SmartFuseBox/SmartFuseBox/KiCad/SmartFuseBox/sheets/Relays.kicad_sch

## KiCad design KiCad/SmartFuseBox/sheets/Relays.kicad_sch (2026-03-11)

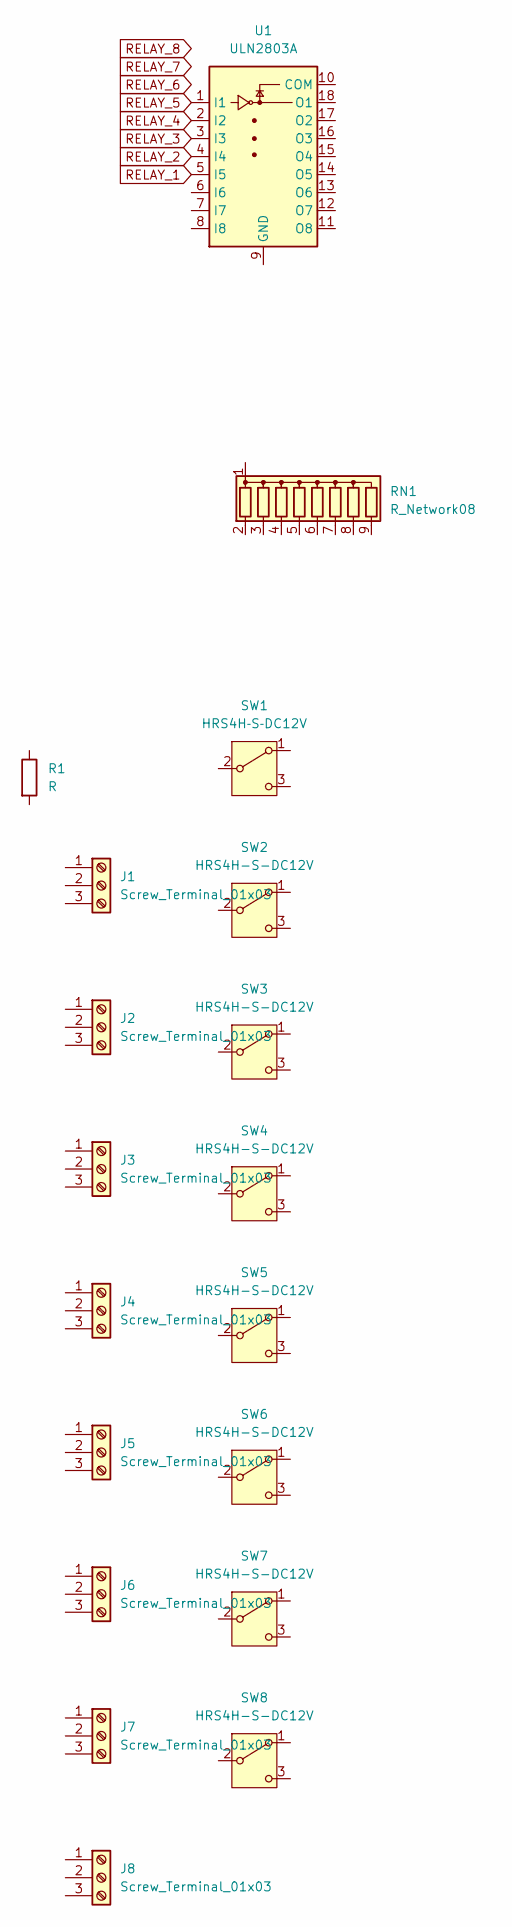
[picture p5: schematic Relays.kicad_sch]

Parts:
J1, J2, J3, J4, J5, J6, J7, J8: Screw_Terminal_01x03
R1: R
RN1: R_Network08; R_Array_SIP9
SW1: HRS4H‑S‑DC12V
SW2, SW3, SW4, SW5, SW6, SW7, SW8: HRS4H-S-DC12V
U1: ULN2803A

Connections:
RELAY_1: U1.5 (I5)
RELAY_2: U1.4 (I4)
RELAY_3: U1.3 (I3)
RELAY_4: U1.2 (I2)
RELAY_5: U1.1 (I1)
