SmartFuseBox/SmartFuseBox/PowerControlHub/PowerControlHub.ino

/*
 * PowerControlHub
 * Copyright (C) 2025 Simon Carter (s1cart3r@gmail.com)
 *
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
 * You should have received a copy of the GNU General Public License
 * along with this program. If not, see <https://www.gnu.org/licenses/>.
 */
#include <Arduino.h>
#include <SerialCommandManager.h>

#include "Local.h"
#include "PowerControlHubApp.h"
#include "SystemFunctions.h"

#include "WaterSensorHandler.h"
#include "Dht11SensorHandler.h"
#include "LightSensorHandler.h"
#include "SystemSensorHandler.h"

 // Hardware UART selection. Change this define if your board routes its serial
// port differently.
// COMPUTER_SERIAL – connected to the host PC / debug monitor.
#define COMPUTER_SERIAL Serial

// forward declares
void onComputerCommandReceived(SerialCommandManager* mgr);


// Consumer note:
// - `commandMgrComputer` is local to your .ino so you can select the hardware
//   Serial instance and baud rate appropriate for your board. Keep the callback
//   `onComputerCommandReceived` in this file so it can access the serial manager.
// - Construct `PowerControlHubApp` with a pointer to the serial manager, then
//   call `app.setup()`. GPS and Nextion serial ports are initialised automatically
//   from persisted config (SensorEntry pins/uartNum and NextionConfig respectively).
// - Call `app.loop()` from `loop()`.

SerialCommandManager commandMgrComputer(&COMPUTER_SERIAL, onComputerCommandReceived, '\n', ':', ';', '=', 500, 64);

PowerControlHubApp app(&commandMgrComputer);

void powerControlHubTask(void* pvParameters)
{
	PowerControlHubApp* app = (PowerControlHubApp*)pvParameters;
	while (true)
	{
		app->loop();
		vTaskDelay(1);
	}
}

void setup()
{
	// Serial initialization is performed first to ensure that any logging or error messages
	// from DateTimeManager or ConfigManager during initialization are properly output.
	SystemFunctions::initializeSerial(COMPUTER_SERIAL, 115200, true);

	SystemFunctions::configureAdc();

	// configure app
	app.setup(nullptr, 0);

	// Create a dedicated task with 16KB stack
	xTaskCreatePinnedToCore(
		powerControlHubTask,
		"PowerControlHub",
		16384,           // stack size
		&app,            // parameters
		1,               // priority
		NULL,            // task handle
		1                // core 1
	);
}

void loop()
{
	vTaskDelay(portMAX_DELAY);
}

// Called when a command arrives on COMPUTER_SERIAL that no registered handler
// claimed. Reports the unrecognised message back to the sender as an error and
// resets the serial buffer to discard any partial frame that may follow.
void onComputerCommandReceived(SerialCommandManager* mgr)
{
	commandMgrComputer.sendError(mgr->getRawMessage(), F("STATCMD"));
	SystemFunctions::resetSerial(COMPUTER_SERIAL);
}
