SmartFuseBox/SmartFuseBox/PowerControlHub/ConfigController.cpp

/*
 * PowerControlHub
 * Copyright (C) 2025 Simon Carter (s1cart3r@gmail.com)
 *
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
 * You should have received a copy of the GNU General Public License
 * along with this program. If not, see <https://www.gnu.org/licenses/>.
 */
#include "ConfigController.h"
#include "SystemDefinitions.h"
#include "RelayController.h"
#include "IBluetoothRadio.h"
#include "IWifiController.h"
#include "SystemFunctions.h"
#include "DateTimeManager.h"

// from NextionIds.h
constexpr uint8_t ImageButtonColorBlue = 2;
constexpr uint8_t ImageButtonColorYellow = 7;


ConfigController::ConfigController(SoundController* soundController, 
	IBluetoothRadio* bluetoothRadio,
	IWifiController* wifiController)
	: _soundController(soundController),
	_bluetoothRadio(bluetoothRadio),
	_wifiController(wifiController),
	_config(nullptr)
{
	_config = ConfigManager::getConfigPtr();
}

Config* ConfigController::getConfigPtr()
{
	return _config;
}

ConfigResult ConfigController::save()
{
	if (_config == nullptr)
		return ConfigResult::InvalidConfig;

	return ConfigManager::save() ? ConfigResult::Success : ConfigResult::Failed;
}

ConfigResult ConfigController::reset()
{
	if (_config == nullptr)
		return ConfigResult::InvalidConfig;

	ConfigManager::resetToDefaults();
	return ConfigResult::Success;
}

ConfigResult ConfigController::rename(const char* name)
{
	if (_config == nullptr)
		return ConfigResult::InvalidConfig;

	if (name == nullptr)
		return ConfigResult::InvalidParameter;

	if (strlen(name) > ConfigMaxNameLength)
		return ConfigResult::TooLong;

	strncpy(_config->location.name, name, sizeof(_config->location.name) - 1);
	_config->location.name[sizeof(_config->location.name) - 1] = '\0';
	return ConfigResult::Success;
}

ConfigResult ConfigController::mapHomeButton(const uint8_t homeButtonIndex, const uint8_t relayIndex)
{
	if (_config == nullptr)
		return ConfigResult::InvalidCommand;

	if (homeButtonIndex >= ConfigHomeButtons)
		return ConfigResult::InvalidParameter;
	
	if (relayIndex >= ConfigRelayCount)
		return ConfigResult::InvalidRelay;

	_config->relay.homePageMapping[homeButtonIndex] = relayIndex;
	return ConfigResult::Success;
}

ConfigResult ConfigController::setLocationType(const uint8_t locationlType)
{
	if (_config == nullptr)
		return ConfigResult::InvalidConfig;
	_config->location.locationType = static_cast<LocationType>(locationlType);
	updateSoundControllerConfig();
	return ConfigResult::Success;
}

void ConfigController::updateSoundControllerConfig()
{
	if (_soundController != nullptr && _config != nullptr)
	{
		_soundController->configUpdated(_config);
	}
}

ConfigResult ConfigController::setsoundDelayStart(const uint16_t delayMilliSeconds)
{
	if (_config == nullptr)
		return ConfigResult::InvalidConfig;

	_config->sound.startDelayMs = delayMilliSeconds;
	updateSoundControllerConfig();
	return ConfigResult::Success;
}

ConfigResult ConfigController::setBluetoothEnabled(const bool enabled)
{
	if (_config == nullptr)
		return ConfigResult::InvalidConfig;

	_config->network.bluetoothEnabled = enabled;

	// do not apply live, only on next restart, otherwise too many enabled/disable cycles will 
	// eventually force the board to run out of memory, the only exception to this is if 
	// it starts disabled and is being enabled now, i.e. once on it needs rebooting to turn off again
	if (_bluetoothRadio && !_bluetoothRadio->isEnabled())
	{
		if (!_bluetoothRadio->setEnabled(enabled))
		{
			return ConfigResult::BluetoothInitFailed;
		}
	}

	return ConfigResult::Success;
}

ConfigResult ConfigController::setWifiEnabled(const bool enabled)
{
	if (_config == nullptr)
		return ConfigResult::InvalidConfig;

	_config->network.wifiEnabled = enabled;

	// do not apply live, only on next restart, otherwise too many enabled/disable cycles will 
	// eventually force the board to run out of memory, the only exception to this is if 
	// it starts disabled and is being enabled now, i.e. once on it needs rebooting to turn off again
	if (_wifiController && !_wifiController->isEnabled())
	{
		if (!_wifiController->setEnabled(enabled))
		{
			return ConfigResult::WifiInitFailed;
		}
	}

	return ConfigResult::Success;
}

ConfigResult ConfigController::setWifiAccessMode(const WifiMode accessMode)
{
	if (_config == nullptr)
		return ConfigResult::InvalidConfig;

	// only accept supported WiFi modes to avoid persisting invalid values from user input
	if (accessMode != WifiMode::AccessPoint && accessMode != WifiMode::Client)
		return ConfigResult::InvalidParameter;
	_config->network.accessMode = accessMode;
	return ConfigResult::Success;
}

ConfigResult ConfigController::setWifiSsid(const char* ssid)
{
	if (_config == nullptr || ssid == nullptr)
		return ConfigResult::InvalidConfig;

	if (strlen(ssid) > MaxSSIDLength - 1)
		return ConfigResult::TooLong;

	strncpy(_config->network.ssid, ssid, sizeof(_config->network.ssid) - 1);
	_config->network.ssid[sizeof(_config->network.ssid) - 1] = '\0';
	return ConfigResult::Success;
}

ConfigResult ConfigController::setWifiPassword(const char* password)
{
	if (_config == nullptr)
		return ConfigResult::InvalidConfig;

	if (password == nullptr)
		return ConfigResult::InvalidParameter;

	if (strlen(password) > MaxWiFiPasswordLength - 1)
		return ConfigResult::InvalidParameter;

	strncpy(_config->network.password, password, sizeof(_config->network.password) - 1);
	_config->network.password[sizeof(_config->network.password) - 1] = '\0';
	return ConfigResult::Success;
}

ConfigResult ConfigController::setWifiPort(const uint16_t port)
{
	if (_config == nullptr)
		return ConfigResult::InvalidConfig;

	if (port == 0)
	{
		return ConfigResult::InvalidParameter;
	}

	_config->network.port = port;
	return ConfigResult::Success;
}

ConfigResult ConfigController::setWifiIpAddress(const char* ipAddress)
{
	if (_config == nullptr)
		return ConfigResult::InvalidConfig;

	if (ipAddress == nullptr)
		return ConfigResult::InvalidParameter;

	if (strlen(ipAddress) > MaxIpAddressLength - 1)
		return ConfigResult::TooLong;

	IPAddress ip;
	if (!ip.fromString(ipAddress))
	{
		return ConfigResult::InvalidParameter;
	}

	strncpy(_config->network.apIpAddress, ipAddress, sizeof(_config->network.apIpAddress) - 1);
	_config->network.apIpAddress[sizeof(_config->network.apIpAddress) - 1] = '\0';
	return ConfigResult::Success;
}

// C20: Set timezone offset
ConfigResult ConfigController::setTimezoneOffset(const int8_t offset)
{
	if (_config == nullptr)
		return ConfigResult::InvalidConfig;

	// Validate range: -12 to +14 hours
	if (offset < -12 || offset > 14)
		return ConfigResult::InvalidParameter;

	_config->system.timezoneOffset = offset;
	DateTimeManager::setTimezoneOffset(offset);
	return ConfigResult::Success;
}

// C21: Set MMSI
ConfigResult ConfigController::setMmsi(const char* mmsi)
{
	if (_config == nullptr)
		return ConfigResult::InvalidConfig;

	if (mmsi == nullptr)
		return ConfigResult::InvalidParameter;

	// Validate MMSI is exactly 9 digits
	size_t len = strlen(mmsi);
	if (len != 9)
		return ConfigResult::InvalidParameter;

	for (size_t i = 0; i < len; i++)
	{
		if (!isdigit(mmsi[i]))
			return ConfigResult::InvalidParameter;
	}

	strncpy(_config->location.mmsi, mmsi, sizeof(_config->location.mmsi) - 1);
	_config->location.mmsi[sizeof(_config->location.mmsi) - 1] = '\0';
	return ConfigResult::Success;
}

// C22: Set call sign
ConfigResult ConfigController::setCallSign(const char* callSign)
{
	if (_config == nullptr)
		return ConfigResult::InvalidConfig;

	if (callSign == nullptr)
		return ConfigResult::InvalidParameter;

	strncpy(_config->location.callSign, callSign, sizeof(_config->location.callSign) - 1);
	_config->location.callSign[sizeof(_config->location.callSign) - 1] = '\0';
	return ConfigResult::Success;
}

// C23: Set home port
ConfigResult ConfigController::setHomePort(const char* homePort)
{
	if (_config == nullptr)
		return ConfigResult::InvalidConfig;

	if (homePort == nullptr)
		return ConfigResult::InvalidParameter;

	strncpy(_config->location.homePort, homePort, sizeof(_config->location.homePort) - 1);
	_config->location.homePort[sizeof(_config->location.homePort) - 1] = '\0';
	return ConfigResult::Success;
}

// C24: Set LED RGB color
ConfigResult ConfigController::setLedColor(const uint8_t type, const uint8_t colorSet, 
										   const uint8_t r, const uint8_t g, const uint8_t b)
{
	if (_config == nullptr)
		return ConfigResult::InvalidConfig;

	// type: 0=day, 1=night
	// colorSet: 0=good, 1=bad
	if (type > 1 || colorSet > 1)
		return ConfigResult::InvalidParameter;

	if (type == 0) // Day mode
	{
		if (colorSet == 0) // Good color
		{
			_config->led.dayGoodColor[0] = r;
			_config->led.dayGoodColor[1] = g;
			_config->led.dayGoodColor[2] = b;
		}
		else // Bad color
		{
			_config->led.dayBadColor[0] = r;
			_config->led.dayBadColor[1] = g;
			_config->led.dayBadColor[2] = b;
		}
	}
	else // Night mode
	{
		if (colorSet == 0) // Good color
		{
			_config->led.nightGoodColor[0] = r;
			_config->led.nightGoodColor[1] = g;
			_config->led.nightGoodColor[2] = b;
		}
		else // Bad color
		{
			_config->led.nightBadColor[0] = r;
			_config->led.nightBadColor[1] = g;
			_config->led.nightBadColor[2] = b;
		}
	}

	return ConfigResult::Success;
}

// C25: Set LED brightness
ConfigResult ConfigController::setLedBrightness(const uint8_t type, const uint8_t brightness)
{
	if (_config == nullptr)
		return ConfigResult::InvalidConfig;

	// type: 0=day, 1=night
	// brightness: 0-100
	if (type > 1 || brightness > 100)
		return ConfigResult::InvalidParameter;

	if (type == 0)
		_config->led.dayBrightness = brightness;
	else
		_config->led.nightBrightness = brightness;

	return ConfigResult::Success;
}

// C26: Set LED auto-switch
ConfigResult ConfigController::setLedAutoSwitch(const bool enabled)
{
	if (_config == nullptr)
		return ConfigResult::InvalidConfig;

	_config->led.autoSwitch = enabled;
	return ConfigResult::Success;
}

// C27: Set LED enable states
ConfigResult ConfigController::setLedEnableStates(const bool gps, const bool warning, const bool system)
{
	if (_config == nullptr)
		return ConfigResult::InvalidConfig;

	_config->led.gpsEnabled = gps;
	_config->led.warningEnabled = warning;
	_config->led.systemEnabled = system;

	return ConfigResult::Success;
}

// C28: Set control panel tones
ConfigResult ConfigController::setControlPanelTones(const uint8_t type, const uint8_t preset, 
													const uint16_t toneHz, const uint16_t durationMs, 
													const uint32_t repeatMs)
{
	if (_config == nullptr)
		return ConfigResult::InvalidConfig;

	// type: 0=good, 1=bad
	if (type > 1)
		return ConfigResult::InvalidParameter;

	// preset: 0=custom, 1=submarine ping, 2=double beep, 3=rising chirp, 
	//         4=descending alert, 5=nautical bell, 0xFFFF=no sound
	// For preset validation, we allow 0-5 or 0xFFFF (65535)
	if (preset > 5 && preset != 0xFF)
		return ConfigResult::InvalidParameter;

	if (type == 0) // Good tone
	{
		_config->sound.goodPreset = preset;
		_config->sound.goodToneHz = toneHz;
		_config->sound.goodDurationMs = durationMs;
		// repeat is only for bad sounds, ignore for good
	}
	else // Bad tone
	{
		_config->sound.badPreset = preset;
		_config->sound.badToneHz = toneHz;
		_config->sound.badDurationMs = durationMs;
		_config->sound.badRepeatMs = repeatMs;
	}

	return ConfigResult::Success;
}

// C31: Set SD card initialize speed
ConfigResult ConfigController::setSdCardInitializeSpeed(const uint8_t speedMhz)
{
	if (_config == nullptr)
		return ConfigResult::InvalidConfig;

	// Only allow specific valid speeds: 4, 8, 12, 16, 20, 24 MHz
	if (speedMhz != 4 && speedMhz != 8 && speedMhz != 12 && 
		speedMhz != 16 && speedMhz != 20 && speedMhz != 24)
		return ConfigResult::InvalidParameter;

	_config->sdCard.initializeSpeed = speedMhz;
	return ConfigResult::Success;
}

// C32: Set SD card CS pin
ConfigResult ConfigController::setSdCardCsPin(const uint8_t csPin)
{
	if (_config == nullptr)
		return ConfigResult::InvalidConfig;

	if (PinGuard::isBlocked(PinGuard::validate(csPin, PinUse::SpiCs)))
		return ConfigResult::InvalidPin;

	_config->sdCard.csPin = csPin;
	return ConfigResult::Success;
}

// C4: Set SPI pins
ConfigResult ConfigController::setSpiPins(const uint8_t sckPin, const uint8_t mosiPin, const uint8_t misoPin)
{
	if (_config == nullptr)
		return ConfigResult::InvalidConfig;

	if (PinGuard::isBlocked(PinGuard::validate(sckPin, PinUse::SpiSck)) ||
		PinGuard::isBlocked(PinGuard::validate(mosiPin, PinUse::SpiMosi)) ||
		PinGuard::isBlocked(PinGuard::validate(misoPin, PinUse::SpiMiso)))
	{
		return ConfigResult::InvalidPin;
	}

	_config->spiPins.sckPin = sckPin;
	_config->spiPins.mosiPin = mosiPin;
	_config->spiPins.misoPin = misoPin;
	return ConfigResult::Success;
}

// C33: Set light sensor daytime threshold
ConfigResult ConfigController::setLightSensorThreshold(const uint16_t threshold)
{
	if (_config == nullptr)
		return ConfigResult::InvalidConfig;

	if (threshold > 1023)
		return ConfigResult::InvalidParameter;

	_config->lightSensor.daytimeThreshold = threshold;
	return ConfigResult::Success;
}

// C6: Set XpdzTone pin
ConfigResult ConfigController::setXpdzTonePin(const uint8_t pin)
{
	if (_config == nullptr)
		return ConfigResult::InvalidConfig;

	if (PinGuard::isBlocked(PinGuard::validate(pin, PinUse::Output)))
		return ConfigResult::InvalidPin;

	_config->xpdzTone.pin = pin;
	return ConfigResult::Success;
}

// C8: Set Hw479Rgb RGB LED pins
ConfigResult ConfigController::setHw479RgbPins(const uint8_t rPin, const uint8_t gPin, const uint8_t bPin)
{
	if (_config == nullptr)
		return ConfigResult::InvalidConfig;

	if (PinGuard::isBlocked(PinGuard::validate(rPin, PinUse::Output)) ||
		PinGuard::isBlocked(PinGuard::validate(gPin, PinUse::Output)) ||
		PinGuard::isBlocked(PinGuard::validate(bPin, PinUse::Output)))
	{
		return ConfigResult::InvalidPin;
	}

	_config->hw479Rgb.rPin = rPin;
	_config->hw479Rgb.gPin = gPin;
	_config->hw479Rgb.bPin = bPin;
	return ConfigResult::Success;
}

// C18: Set RtcConfig DS1302 pins
ConfigResult ConfigController::setRtcPins(const uint8_t dataPin, const uint8_t clockPin, const uint8_t resetPin)
{
	if (_config == nullptr)
		return ConfigResult::InvalidConfig;

	// Temporarily clear current RTC pin assignments so they don't
	// conflict with themselves during validation (getUsedPins collects
	// the current rtc.dataPin/clockPin/resetPin values).
	const uint8_t oldData = _config->rtc.dataPin;
	const uint8_t oldClock = _config->rtc.clockPin;
	const uint8_t oldReset = _config->rtc.resetPin;

	_config->rtc.dataPin = PinDisabled;
	_config->rtc.clockPin = PinDisabled;
	_config->rtc.resetPin = PinDisabled;

	const bool blocked = PinGuard::isBlocked(PinGuard::validate(dataPin, PinUse::Output))
		|| PinGuard::isBlocked(PinGuard::validate(clockPin, PinUse::Output))
		|| PinGuard::isBlocked(PinGuard::validate(resetPin, PinUse::Output));

	if (blocked)
	{
		// Restore old values on failure
		_config->rtc.dataPin = oldData;
		_config->rtc.clockPin = oldClock;
		_config->rtc.resetPin = oldReset;
		return ConfigResult::InvalidPin;
	}

	_config->rtc.dataPin = dataPin;
	_config->rtc.clockPin = clockPin;
	_config->rtc.resetPin = resetPin;
	return ConfigResult::Success;
}

// C19 (N commands): Set NextionConfig display configuration — individual setters
ConfigResult ConfigController::setNextionEnabled(const bool enabled)
{
	if (_config == nullptr)
		return ConfigResult::InvalidConfig;

	_config->nextion.enabled = enabled;
	return ConfigResult::Success;
}

ConfigResult ConfigController::setNextionHardwareSerial(const bool isHardwareSerial)
{
	if (_config == nullptr)
		return ConfigResult::InvalidConfig;

	_config->nextion.isHardwareSerial = isHardwareSerial;
	return ConfigResult::Success;
}

ConfigResult ConfigController::setNextionRxPin(const uint8_t rxPin)
{
	if (_config == nullptr)
		return ConfigResult::InvalidConfig;

	if (PinGuard::isBlocked(PinGuard::validate(rxPin, PinUse::Input)))
		return ConfigResult::InvalidPin;

	_config->nextion.rxPin = rxPin;
	return ConfigResult::Success;
}

ConfigResult ConfigController::setNextionTxPin(const uint8_t txPin)
{
	if (_config == nullptr)
		return ConfigResult::InvalidConfig;

	if (PinGuard::isBlocked(PinGuard::validate(txPin, PinUse::Output)))
		return ConfigResult::InvalidPin;

	_config->nextion.txPin = txPin;
	return ConfigResult::Success;
}

ConfigResult ConfigController::setNextionBaudRate(const uint32_t baudRate)
{
	if (_config == nullptr)
		return ConfigResult::InvalidConfig;

	_config->nextion.baudRate = baudRate;
	return ConfigResult::Success;
}

ConfigResult ConfigController::setNextionUartNum(const uint8_t uartNum)
{
    if (_config == nullptr)
        return ConfigResult::InvalidConfig;

    if (uartNum != 1 && uartNum != 2)
        return ConfigResult::InvalidParameter;

    _config->nextion.uartNum = uartNum;
    return ConfigResult::Success;
}

// Generate device-unique API and HMAC keys and store them in config.auth
ConfigResult ConfigController::generateAuthKeys()
{
    if (_config == nullptr)
        return ConfigResult::InvalidConfig;

    char deviceId[26];
    deviceId[0] = '\0';

    if (SystemFunctions::GenerateDefaultPassword(deviceId, sizeof(deviceId)) != BufferSuccess)
        return ConfigResult::Failed;

    // apiKey = "ak-" + deviceId, hmacKey = "hk-" + deviceId
    char apiKey[ConfigAuthApiKeyLength];
    char hmacKey[ConfigAuthHmacKeyLength];

    snprintf(apiKey, sizeof(apiKey), "ak-%s", deviceId);
    apiKey[sizeof(apiKey) - 1] = '\0';

    snprintf(hmacKey, sizeof(hmacKey), "hk-%s", deviceId);
    hmacKey[sizeof(hmacKey) - 1] = '\0';

    strncpy(_config->auth.apiKey, apiKey, sizeof(_config->auth.apiKey) - 1);
    _config->auth.apiKey[sizeof(_config->auth.apiKey) - 1] = '\0';

    strncpy(_config->auth.hmacKey, hmacKey, sizeof(_config->auth.hmacKey) - 1);
    _config->auth.hmacKey[sizeof(_config->auth.hmacKey) - 1] = '\0';

    return ConfigResult::Success;
}

ConfigResult ConfigController::setAuthEnabled(const bool enabled)
{
    if (_config == nullptr)
        return ConfigResult::InvalidConfig;

	if (enabled && (strlen(_config->auth.apiKey) == 0 || strlen(_config->auth.hmacKey) == 0))
	{
		return ConfigResult::InvalidParameter;
	}

    _config->auth.enabled = enabled;

    return ConfigResult::Success;
}

ConfigResult ConfigController::setAuthApiKey(const char* apiKey)
{
    if (_config == nullptr)
        return ConfigResult::InvalidConfig;

	if (apiKey == nullptr)
	{
		setAuthEnabled(false);
		return ConfigResult::InvalidParameter;
	}

	if (strlen(apiKey) > ConfigAuthApiKeyLength - 1)
	{
		setAuthEnabled(false);
		return ConfigResult::TooLong;
	}

    strncpy(_config->auth.apiKey, apiKey, sizeof(_config->auth.apiKey) - 1);
    _config->auth.apiKey[sizeof(_config->auth.apiKey) - 1] = '\0';

    return ConfigResult::Success;
}

ConfigResult ConfigController::setAuthHmacKey(const char* hmacKey)
{
    if (_config == nullptr)
        return ConfigResult::InvalidConfig;

	if (hmacKey == nullptr)
	{
		setAuthEnabled(false);
		return ConfigResult::InvalidParameter;
	}

	if (strlen(hmacKey) > ConfigAuthHmacKeyLength - 1)
	{
		setAuthEnabled(false);
		return ConfigResult::TooLong;
	}

    strncpy(_config->auth.hmacKey, hmacKey, sizeof(_config->auth.hmacKey) - 1);
    _config->auth.hmacKey[sizeof(_config->auth.hmacKey) - 1] = '\0';

    return ConfigResult::Success;
}
