SmartFuseBox/SmartFuseBox/PowerControlHub/ConfigCommandHandler.cpp

/*
 * PowerControlHub
 * Copyright (C) 2025 Simon Carter (s1cart3r@gmail.com)
 *
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
 * You should have received a copy of the GNU General Public License
 * along with this program. If not, see <https://www.gnu.org/licenses/>.
 */
#include <Arduino.h>
#include "ConfigCommandHandler.h"
#include "ConfigController.h"
#include "SystemFunctions.h"
#include "MessageBus.h"

#if defined(CARD_CONFIG_LOADER)
#include "SdCardConfigLoader.h"
#endif

#if defined(MQTT_SUPPORT)
#include "MQTTConfigCommandHandler.h"
#include "MQTTController.h"
#endif


ConfigCommandHandler::ConfigCommandHandler(
	IWifiController* wifiController,
	ConfigController* configController)
	:
	_wifiController(wifiController),
	_configController(configController),
	_messageBus(nullptr)
#if defined(CARD_CONFIG_LOADER)
	, _sdCardConfigLoader(nullptr)
#endif
#if defined(MQTT_SUPPORT)
	, _mqttConfigHandler(nullptr)
	, _mqttController(nullptr)
#endif
{}

void ConfigCommandHandler::setMessageBus(MessageBus* messageBus)
{
	_messageBus = messageBus;
}

#if defined(MQTT_SUPPORT)
void ConfigCommandHandler::setMqttConfigHandler(MQTTConfigCommandHandler* mqttConfigHandler)
{
	_mqttConfigHandler = mqttConfigHandler;
}

void ConfigCommandHandler::setMqttController(MQTTController* mqttController)
{
	_mqttController = mqttController;
}
#endif

bool ConfigCommandHandler::handleCommand(SerialCommandManager* sender, const char* command, const StringKeyValue params[], uint8_t paramCount)
{
	// Access the in-memory config
	ConfigResult result;

	if (SystemFunctions::commandMatches(command, ConfigSaveSettings))
	{
		result = _configController->save();

		if (result == ConfigResult::Success)
		{
			const char* rebootStr = getParamValue(params, paramCount, "reboot");
			if (rebootStr && SystemFunctions::parseBooleanValue(rebootStr))
			{
				if (SystemFunctions::canReboot() && _messageBus != nullptr)
				{
					char rebootVal[] = "pending";
					StringKeyValue rebootParam = makeParam("reboot", rebootVal);
					sendAckOk(sender, command, &rebootParam);
					_messageBus->publish<RebootRequested>();
					return true;
				}
				else
				{
					char rebootVal[] = "required";
					StringKeyValue rebootParam = makeParam("reboot", rebootVal);
					sendAckOk(sender, command, &rebootParam);
					return true;
				}
			}
		}
	}
	else if (SystemFunctions::commandMatches(command, ConfigGetSettings))
	{
		char buffer[128]{};
		buffer[0] = '\0';

		Config* config = _configController->getConfigPtr();

		if (!config)
		{
			sendAckErr(sender, command, F("Config not available"));
			return true;
		}

		// return summary of config back to caller in multiple commands
		// C3:<name>
		sender->sendCommand(ConfigRename, config->location.name);

		// C4 SPI pins
		snprintf(buffer, sizeof(buffer), "sck=%u;mosi=%u;miso=%u",
			config->spiPins.sckPin,
			config->spiPins.mosiPin,
			config->spiPins.misoPin);
		sender->sendCommand(ConfigSpiPins, buffer);

		// C5 entries
		for (uint8_t s = 0; s < ConfigHomeButtons; ++s)
		{
			snprintf(buffer, sizeof(buffer), "%u=%u", s, config->relay.homePageMapping[s]);
			sender->sendCommand(ConfigMapHomeButton, buffer);
		}

		// C6 XpdzTone pin
		snprintf(buffer, sizeof(buffer), "v=%u", config->xpdzTone.pin);
		sender->sendCommand(ConfigXpdzTonePin, buffer);

		// C7 Boat type
		snprintf(buffer, sizeof(buffer), "v=%d", static_cast<uint8_t>(config->location.locationType));
		sender->sendCommand(ConfigBoatType, buffer);

		// C8 Hw479Rgb pins
		snprintf(buffer, sizeof(buffer), "r=%u;g=%u;b=%u",
			config->hw479Rgb.rPin,
			config->hw479Rgb.gPin,
			config->hw479Rgb.bPin);
		sender->sendCommand(ConfigHw479RgbPins, buffer);

		// C9 Sound start delay
		snprintf(buffer, sizeof(buffer), "v=%u", static_cast<unsigned int>(config->sound.startDelayMs));
		sender->sendCommand(ConfigSoundStartDelay, buffer);

		// C10 Bluetooth enable
		snprintf(buffer, sizeof(buffer), "v=%s", (config->network.bluetoothEnabled ? "1" : "0"));
		sender->sendCommand(ConfigBluetoothEnable, buffer);

		// C11 WiFi enable
		snprintf(buffer, sizeof(buffer), "v=%s", (config->network.wifiEnabled ? "1" : "0"));
		sender->sendCommand(ConfigWifiEnable, buffer);

		// C12 WiFi mode
		snprintf(buffer, sizeof(buffer), "v=%d", static_cast<uint8_t>(config->network.accessMode));
		sender->sendCommand(ConfigWifiMode, buffer);

		// C13 WiFi SSID
		snprintf(buffer, sizeof(buffer), "v=%s", config->network.ssid);
		sender->sendCommand(ConfigWifiSSID, buffer);

		// C14 WiFi Password
		snprintf(buffer, sizeof(buffer), "v=%s", config->network.password);
		sender->sendCommand(ConfigWifiPassword, buffer);

		// C15 WiFi Port
		snprintf(buffer, sizeof(buffer), "v=%d", config->network.port);
		sender->sendCommand(ConfigWifiPort, buffer);

		// C16 WiFi State
		if (_wifiController)
		{
			snprintf(buffer, sizeof(buffer), "v=%d", static_cast<int>(_wifiController->getConnectionState()));
			sender->sendCommand(ConfigWifiState, buffer);
		}

		// C17 WiFi AP IP Address
		if (_wifiController)
		{
			char ipBuffer[MaxIpAddressLength];
			_wifiController->getIpAddress(ipBuffer, sizeof(ipBuffer));
			snprintf(buffer, sizeof(buffer), "v=%s", ipBuffer);
			sender->sendCommand(ConfigWifiApIpAddress, buffer);
		}

		// C18 RTC pins
		snprintf(buffer, sizeof(buffer), "dat=%u;clk=%u;rst=%u",
			config->rtc.dataPin,
			config->rtc.clockPin,
			config->rtc.resetPin);
		sender->sendCommand(ConfigRtcPins, buffer);

		// C19 Network auth
		snprintf(buffer, sizeof(buffer), "e=%d;k=%s;h=%s",
			config->auth.enabled ? 1 : 0,
			config->auth.apiKey,
			config->auth.hmacKey);
		sender->sendCommand(ConfigAuthCommand, buffer);

		// N1–N6 Nextion display config (broadcast as individual commands)
		snprintf(buffer, sizeof(buffer), "v=%u", config->nextion.enabled ? 1u : 0u);
		sender->sendCommand(NextionEnabled, buffer);

		snprintf(buffer, sizeof(buffer), "v=%u", config->nextion.isHardwareSerial ? 1u : 0u);
		sender->sendCommand(NextionHardwareSerial, buffer);

		snprintf(buffer, sizeof(buffer), "v=%u", config->nextion.rxPin);
		sender->sendCommand(NextionRxPin, buffer);

		snprintf(buffer, sizeof(buffer), "v=%u", config->nextion.txPin);
		sender->sendCommand(NextionTxPin, buffer);

		snprintf(buffer, sizeof(buffer), "v=%lu", config->nextion.baudRate);
		sender->sendCommand(NextionBaudRate, buffer);

		snprintf(buffer, sizeof(buffer), "v=%u", config->nextion.uartNum);
		sender->sendCommand(NextionUartNum, buffer);

		// C20 Timezone offset
		snprintf(buffer, sizeof(buffer), "v=%d", config->system.timezoneOffset);
		sender->sendCommand(ConfigTimeZoneOffset, buffer);

		// C21 MMSI
		sender->sendCommand(ConfigMmsi, config->location.mmsi);

		// C22 Call sign
		sender->sendCommand(ConfigCallSign, config->location.callSign);

		// C23 Home port
		sender->sendCommand(ConfigHomePort, config->location.homePort);

		// C24 LED Colors (send all 4: day/good, day/bad, night/good, night/bad)
		// Day mode, good color
		snprintf(buffer, sizeof(buffer), "t=0;c=0;r=%u;g=%u;b=%u",
			config->led.dayGoodColor[0],
			config->led.dayGoodColor[1],
			config->led.dayGoodColor[2]);
		sender->sendCommand(ConfigLedColor, buffer);

		// Day mode, bad color
		snprintf(buffer, sizeof(buffer), "t=0;c=1;r=%u;g=%u;b=%u",
			config->led.dayBadColor[0],
			config->led.dayBadColor[1],
			config->led.dayBadColor[2]);
		sender->sendCommand(ConfigLedColor, buffer);

		// Night mode, good color
		snprintf(buffer, sizeof(buffer), "t=1;c=0;r=%u;g=%u;b=%u",
			config->led.nightGoodColor[0],
			config->led.nightGoodColor[1],
			config->led.nightGoodColor[2]);
		sender->sendCommand(ConfigLedColor, buffer);

		// Night mode, bad color
		snprintf(buffer, sizeof(buffer), "t=1;c=1;r=%u;g=%u;b=%u",
			config->led.nightBadColor[0],
			config->led.nightBadColor[1],
			config->led.nightBadColor[2]);
		sender->sendCommand(ConfigLedColor, buffer);

		// C25 LED Brightness (send both day and night)
		snprintf(buffer, sizeof(buffer), "t=0;b=%u", config->led.dayBrightness);
		sender->sendCommand(ConfigLedBrightness, buffer);

		snprintf(buffer, sizeof(buffer), "t=1;b=%u", config->led.nightBrightness);
		sender->sendCommand(ConfigLedBrightness, buffer);

		// C26 LED Auto-switch
		snprintf(buffer, sizeof(buffer), "v=%s", config->led.autoSwitch ? "1" : "0");
		sender->sendCommand(ConfigLedAutoSwitch, buffer);

		// C27 LED Enable states
		snprintf(buffer, sizeof(buffer), "g=%s;w=%s;s=%s",
			config->led.gpsEnabled ? "1" : "0",
			config->led.warningEnabled ? "1" : "0",
			config->led.systemEnabled ? "1" : "0");
		sender->sendCommand(ConfigLedEnable, buffer);

		// C28 Control Panel Tones - Good tone
		snprintf(buffer, sizeof(buffer), "t=0;h=%u;d=%u;p=%u;r=0",
			config->sound.goodToneHz,
			config->sound.goodDurationMs,
			config->sound.goodPreset);
		sender->sendCommand(ControlPanelTones, buffer);

		// C28 Control Panel Tones - Bad tone
		snprintf(buffer, sizeof(buffer), "t=1;h=%u;d=%u;p=%u;r=%lu",
			config->sound.badToneHz,
			config->sound.badDurationMs,
			config->sound.badPreset,
			config->sound.badRepeatMs);
		sender->sendCommand(ControlPanelTones, buffer);

		// C31 SD Card Initialize Speed
		snprintf(buffer, sizeof(buffer), "v=%u", config->sdCard.initializeSpeed);
		sender->sendCommand(ConfigSdCardSpeed, buffer);

		// C32 SD Card CS pin
		snprintf(buffer, sizeof(buffer), "v=%u", config->sdCard.csPin);
		sender->sendCommand(ConfigSdCardCsPin, buffer);

		// C33 Light sensor daytime threshold
		snprintf(buffer, sizeof(buffer), "v=%u", config->lightSensor.daytimeThreshold);
		sender->sendCommand(ConfigLightSensorThreshold, buffer);

		result = ConfigResult::Success;
	}
	else if (SystemFunctions::commandMatches(command, ConfigResetSettings))
	{
		// Reset to defaults
		result = _configController->reset();
	}
	else if (SystemFunctions::commandMatches(command, ConfigRename))
	{
		if (paramCount >= 1)
		{
			result = _configController->rename(params[0].value);
		}
		else
		{
			result = ConfigResult::InvalidParameter;
		}
	}
	else if (SystemFunctions::commandMatches(command, ConfigMapHomeButton))
	{
		// Expect "MAP <button>=<relay>" where button 0..3, relay 0..7 (or 255 to unmap)
		if (paramCount >= 1)
		{
			uint8_t button = static_cast<uint8_t>(strtoul(params[0].key, nullptr, 0));
			uint8_t relay = static_cast<uint8_t>(strtoul(params[0].value, nullptr, 0));

			result = _configController->mapHomeButton(button, relay);
		}
		else
		{
			result = ConfigResult::InvalidParameter;
		}
	}
	else if (SystemFunctions::commandMatches(command, ConfigXpdzTonePin))
	{
		// C6 - Set XpdzTone pin
		// Format: C6:v=<pin> (use 255/PinDisabled to disable)
		if (paramCount >= 1)
		{
			uint8_t pin;
			if (!getParamValueU8t(params, paramCount, "v", pin))
			{
				result = ConfigResult::InvalidParameter;
			}
			else
			{
				result = _configController->setXpdzTonePin(pin);

				if (result == ConfigResult::InvalidPin)
				{
					char dbg[40];
					snprintf(dbg, sizeof(dbg), "XpdzTone pin %u blocked: %s", pin,
						reinterpret_cast<const char*>(PinGuard::reasonString(PinGuard::validate(pin, PinUse::Output))));
					sender->sendDebug(dbg, "C6");
				}
			}
		}
		else
		{
			result = ConfigResult::InvalidParameter;
		}
	}
  else if (SystemFunctions::commandMatches(command, ConfigSpiPins))
	{
		if (paramCount >= 3)
		{
			uint8_t sckPin, mosiPin, misoPin;
			if (!getParamValueU8t(params, paramCount, "sck", sckPin) ||
				!getParamValueU8t(params, paramCount, "mosi", mosiPin) ||
				!getParamValueU8t(params, paramCount, "miso", misoPin))
			{
				result = ConfigResult::InvalidParameter;
			}
			else
			{
				result = _configController->setSpiPins(sckPin, mosiPin, misoPin);

				if (result == ConfigResult::InvalidPin)
				{
					char dbg[64];
					snprintf(dbg, sizeof(dbg), "SPI pin blocked: sck=%u mosi=%u miso=%u", sckPin, mosiPin, misoPin);
					sender->sendDebug(dbg, "C4");
				}
			}
		}
		else
		{
			result = ConfigResult::InvalidParameter;
		}
	}
	else if (SystemFunctions::commandMatches(command, ConfigBoatType))
	{
		// Expect "C7:type=<value>" where value is 0..3
		if (paramCount >= 1)
		{
			uint8_t type = atoi(params[0].value);
			result = _configController->setLocationType(type);
		}
		else
		{
			result = ConfigResult::InvalidParameter;
		}
	}
	else if (SystemFunctions::commandMatches(command, ConfigHw479RgbPins))
	{
		// C8 - Set Hw479Rgb RGB LED pins
		// Format: C8:r=<pin>;g=<pin>;b=<pin> (use 255/PinDisabled to disable)
		if (paramCount >= 3)
		{
			uint8_t rPin, gPin, bPin;
			if (!getParamValueU8t(params, paramCount, "r", rPin) ||
				!getParamValueU8t(params, paramCount, "g", gPin) ||
				!getParamValueU8t(params, paramCount, "b", bPin))
			{
				result = ConfigResult::InvalidParameter;
			}
			else
			{
				result = _configController->setHw479RgbPins(rPin, gPin, bPin);

				if (result == ConfigResult::InvalidPin)
				{
					char dbg[56];
					snprintf(dbg, sizeof(dbg), "RGB pin blocked: r=%u g=%u b=%u", rPin, gPin, bPin);
					sender->sendDebug(dbg, "C8");
				}
			}
		}
		else
		{
			result = ConfigResult::InvalidParameter;
		}
	}
	else if (SystemFunctions::commandMatches(command, ConfigSoundStartDelay))
	{
		if (paramCount == 1)
		{
			uint16_t soundStartDelay = atoi(params[0].value);
			result = _configController->setsoundDelayStart(soundStartDelay);
		}
		else
		{
			result = ConfigResult::InvalidParameter;
		}
	}
	else if (SystemFunctions::commandMatches(command, ConfigBluetoothEnable))
	{
		// Expect "C10:v=<0|1>"
		if (paramCount >= 1)
		{
			bool enable = SystemFunctions::parseBooleanValue(params[0].value);
			result = _configController->setBluetoothEnabled(enable);
		}
		else
		{
			result = ConfigResult::InvalidParameter;
		}
	}
	else if (SystemFunctions::commandMatches(command, ConfigWifiEnable))
	{
		// Expect "C11:v=<0|1>"
		if (paramCount >= 1)
		{
			bool enable = SystemFunctions::parseBooleanValue(params[0].value);
			result = _configController->setWifiEnabled(enable);
		}
		else
		{
			result = ConfigResult::InvalidParameter;
		}
	}
	else if (SystemFunctions::commandMatches(command, ConfigWifiMode))
	{
		// Expect "C12:v=<0|1>"
		if (paramCount >= 1)
		{
			WifiMode mode = static_cast<WifiMode>(atoi(params[0].value));
			result = _configController->setWifiAccessMode(mode);
		}
		else
		{
			result = ConfigResult::InvalidParameter;
		}
	}
	else if (SystemFunctions::commandMatches(command, ConfigWifiSSID))
	{
		// Expect "C13:v=<value>"
		if (paramCount >= 1)
		{
			result = _configController->setWifiSsid(params[0].value);
		}
		else
		{
			result = ConfigResult::InvalidParameter;
		}
	}
	else if (SystemFunctions::commandMatches(command, ConfigWifiPassword))
	{
		// Expect "C14:v=<value>"
		if (paramCount >= 1)
		{
			result = _configController->setWifiPassword(params[0].value);
		}
		else
		{
			result = ConfigResult::InvalidParameter;
		}
	}
	else if (SystemFunctions::commandMatches(command, ConfigWifiPort))
	{
		// Expect "C15:v=<value>"
		if (paramCount >= 1)
		{
			uint16_t port = static_cast<uint16_t>(atoi(params[0].value));
			result = _configController->setWifiPort(port);
		}
		else
		{
			result = ConfigResult::InvalidParameter;
		}
	}
	else if (SystemFunctions::commandMatches(command, ConfigWifiState))
	{
		// C16 WiFi State
		uint8_t state = static_cast<uint8_t>(WifiConnectionState::Disconnected);

		if (_wifiController)
		{
			state = static_cast<uint8_t>(_wifiController->getConnectionState());
		}

		char cmd[10];
		snprintf(cmd, sizeof(cmd), "v=%d", state);
		sender->sendCommand(ConfigWifiState, cmd);
		result = ConfigResult::Success;
	}
	else if (SystemFunctions::commandMatches(command, ConfigWifiApIpAddress))
	{
		// Expect "C17:v=<value>"
		if (paramCount >= 1)
		{
			result = _configController->setWifiIpAddress(params[0].value);
		}
		else
		{
			result = ConfigResult::InvalidParameter;
		}
	}
	else if (SystemFunctions::commandMatches(command, ConfigRtcPins))
	{
		// C18 - Set RtcConfig DS1302 pins
		// Format: C18:dat=<pin>;clk=<pin>;rst=<pin> (use 255/PinDisabled for any unfit pin)
		if (paramCount >= 3)
		{
			uint8_t dataPin, clockPin, resetPin;
			if (!getParamValueU8t(params, paramCount, "dat", dataPin) ||
				!getParamValueU8t(params, paramCount, "clk", clockPin) ||
				!getParamValueU8t(params, paramCount, "rst", resetPin))
			{
				result = ConfigResult::InvalidParameter;
			}
			else
			{
				result = _configController->setRtcPins(dataPin, clockPin, resetPin);

				if (result == ConfigResult::InvalidPin)
				{
					char dbg[64];
					snprintf(dbg, sizeof(dbg), "RTC pin blocked: dat=%u clk=%u rst=%u", dataPin, clockPin, resetPin);
					sender->sendDebug(dbg, "C18");
				}
			}
		}
		else
		{
			result = ConfigResult::InvalidParameter;
		}
	}
	else if (SystemFunctions::commandMatches(command, ConfigAuthCommand))
	{
		// C19 - Network authentication configuration (repurposed from retired Nextion usage)
		// Params: e=0|1 (enable), k=<apikey>, h=<hmackey>, g=1 (auto-generate keys)
		// No params returns current state
		if (paramCount == 0)
		{
			// Read-only: return current auth state
			Config* config = _configController->getConfigPtr();
			if (config)
			{
				char buffer[128];
				snprintf(buffer, sizeof(buffer), "e=%d;k=%s;h=%s",
					config->auth.enabled ? 1 : 0,
					config->auth.apiKey,
					config->auth.hmacKey);
				sender->sendCommand(ConfigAuthCommand, buffer);
				result = ConfigResult::Success;
			}
			else
			{
				sendAckErr(sender, command, F("Config not available"));
				return true;
			}
		}
		else
		{
			bool generate = false;
			getParamValueBool(params, paramCount, ConfigAuthGenerateParam, generate);

			if (generate)
			{
				result = _configController->generateAuthKeys();
			}
			else
			{
				bool enabled;
				if (getParamValueBool(params, paramCount, ConfigAuthEnabledParam, enabled))
				{
					_configController->setAuthEnabled(enabled);
					result = ConfigResult::Success;
				}

				const char* apiKeyVal = getParamValue(params, paramCount, ConfigAuthApiKeyParam);
				if (apiKeyVal)
				{
					result = _configController->setAuthApiKey(apiKeyVal);

					if (result != ConfigResult::Success)
					{
						sendAckErr(sender, command, "API key too long");
						return true;
					}
				}

				const char* hmacKeyVal = getParamValue(params, paramCount, ConfigAuthHmacKeyParam);
				if (hmacKeyVal)
				{
					result = _configController->setAuthHmacKey(hmacKeyVal);

					if (result != ConfigResult::Success)
					{
						sendAckErr(sender, command, "HMAC key too long");
						return true;
					}
				}
			}
		}
	}
	else if (SystemFunctions::commandMatches(command, ConfigTimeZoneOffset))
	{
		// C20 - Set timezone offset (hours from UTC, -12 to +14)
		// Format: C20:v=-5 or C20:v=8
		if (paramCount >= 1)
		{
			int8_t offset = static_cast<int8_t>(atoi(params[0].value));
			result = _configController->setTimezoneOffset(offset);
		}
		else
		{
			result = ConfigResult::InvalidParameter;
		}
	}
	else if (SystemFunctions::commandMatches(command, ConfigMmsi))
	{
		// C21 - Set MMSI (9 digits)
		// Format: C21:123456789
		if (paramCount >= 1)
		{
			result = _configController->setMmsi(params[0].value);
		}
		else
		{
			result = ConfigResult::InvalidParameter;
		}
	}
	else if (SystemFunctions::commandMatches(command, ConfigCallSign))
	{
		// C22 - Set call sign
		// Format: C22:ABCD123
		if (paramCount >= 1)
		{
			result = _configController->setCallSign(params[0].value);
		}
		else
		{
			result = ConfigResult::InvalidParameter;
		}
	}
	else if (SystemFunctions::commandMatches(command, ConfigHomePort))
	{
		// C23 - Set home port
		// Format: C23:Miami
		if (paramCount >= 1)
		{
			result = _configController->setHomePort(params[0].value);
		}
		else
		{
			result = ConfigResult::InvalidParameter;
		}
	}
	else if (SystemFunctions::commandMatches(command, ConfigLedColor))
	{
		// C24 - Set LED RGB color
		// Format: C24:t=0;c=0;r=255;g=50;b=213
		// t=type (0=day, 1=night), c=colorset (0=good, 1=bad), r/g/b=0-255
		if (paramCount >= 5)
		{
			uint8_t type, colorSet, r, g, b;
			if (!getParamValueU8t(params, paramCount, "t", type) ||
				!getParamValueU8t(params, paramCount, "c", colorSet) ||
				!getParamValueU8t(params, paramCount, "r", r) ||
				!getParamValueU8t(params, paramCount, "g", g) ||
				!getParamValueU8t(params, paramCount, "b", b))
			{
				result = ConfigResult::InvalidParameter;
			}
			else
			{
				result = _configController->setLedColor(type, colorSet, r, g, b);
			}
		}
		else
		{
			result = ConfigResult::InvalidParameter;
		}
	}
	else if (SystemFunctions::commandMatches(command, ConfigLedBrightness))
	{
		// C25 - Set LED brightness
		// Format: C25:t=0;b=75
		// t=type (0=day, 1=night), b=brightness (0-100)
		if (paramCount >= 2)
		{
			uint8_t type, brightness;
			if (!getParamValueU8t(params, paramCount, "t", type) ||
				!getParamValueU8t(params, paramCount, "b", brightness))
			{
				result = ConfigResult::InvalidParameter;
			}
			else
			{
				result = _configController->setLedBrightness(type, brightness);
			}
		}
		else
		{
			result = ConfigResult::InvalidParameter;
		}
	}
	else if (SystemFunctions::commandMatches(command, ConfigLedAutoSwitch))
	{
		// C26 - Enable/disable auto day/night switching
		// Format: C26:v=true or C26:v=1
		if (paramCount >= 1)
		{
			bool enabled = SystemFunctions::parseBooleanValue(params[0].value);
			result = _configController->setLedAutoSwitch(enabled);
		}
		else
		{
			result = ConfigResult::InvalidParameter;
		}
	}
	else if (SystemFunctions::commandMatches(command, ConfigLedEnable))
	{
		// C27 - Enable/disable individual LEDs
		// Format: C27:g=true;w=true;s=false
		// g=GPS LED, w=Warning LED, s=System LED
		if (paramCount >= 3)
		{
			bool gps = false;
			bool warning = false;
			bool system = false;

			if (!getParamValueBool(params, paramCount, "g", gps) ||
				!getParamValueBool(params, paramCount, "w", warning) ||
				!getParamValueBool(params, paramCount, "s", system))
			{
				result = ConfigResult::InvalidParameter;
			}

			result = _configController->setLedEnableStates(gps, warning, system);
		}
		else
		{
			result = ConfigResult::InvalidParameter;
		}
	}
	else if (SystemFunctions::commandMatches(command, ControlPanelTones))
	{
		// C28 - Configure control panel tones
		// Format: C28:t=0;h=400;d=500;p=0;r=30000
		// t=type (0=good, 1=bad), h=tone Hz, d=duration ms, p=preset, r=repeat interval ms (bad only)
		if (paramCount >= 4)
		{
			uint8_t type, preset;
			uint16_t toneHz, durationMs;
			uint32_t repeatMs;
			if (!getParamValueU8t(params, paramCount, "t", type) ||
				!getParamValueU8t(params, paramCount, "p", preset) ||
				!getParamValueU16t(params, paramCount, "h", toneHz) ||
				!getParamValueU16t(params, paramCount, "d", durationMs) ||
				!getParamValueU32t(params, paramCount, "r", repeatMs))
			{
				result = ConfigResult::InvalidParameter;
			}
			else
			{
				result = _configController->setControlPanelTones(type, preset, toneHz, durationMs, repeatMs);
			}
		}
		else
		{
			result = ConfigResult::InvalidParameter;
		}
	}
	else if (SystemFunctions::commandMatches(command, ConfigReloadFromSd))
	{
#if defined(CARD_CONFIG_LOADER)
		if (_sdCardConfigLoader)
		{
			if (_sdCardConfigLoader->reloadConfigFromSd())
			{
				result = ConfigResult::Success;
			}
			else
			{
				sendAckErr(sender, command, F("Failed to reload from SD"));
				return true;
			}
		}
		else
		{
			sendAckErr(sender, command, F("SD config loader not available"));
			return true;
		}
#else
		sendAckErr(sender, command, F("SD card not supported"));
		return true;
#endif
	}
	else if (SystemFunctions::commandMatches(command, ConfigExportToSd))
	{
#if defined(CARD_CONFIG_LOADER)
		if (_sdCardConfigLoader)
		{
			if (_sdCardConfigLoader->exportConfigToSd())
			{
				result = ConfigResult::Success;
			}
			else
			{
				sendAckErr(sender, command, F("Failed to export to SD"));
				return true;
			}
		}
		else
		{
			sendAckErr(sender, command, F("SD config loader not available"));
			return true;
		}
#else
		sendAckErr(sender, command, F("SD card not supported"));
		return true;
#endif
	}
	else if (SystemFunctions::commandMatches(command, ConfigSdCardSpeed))
	{
#if defined(SD_CARD_SUPPORT)
		if (paramCount >= 1)
		{
			uint8_t speedMhz = static_cast<uint8_t>(atoi(params[0].value));
			result = _configController->setSdCardInitializeSpeed(speedMhz);
		}
		else
		{
			result = ConfigResult::InvalidParameter;
		}
#else
		sendAckErr(sender, command, F("SD card not supported"));
		return true;
#endif
	}
	else if (SystemFunctions::commandMatches(command, ConfigSdCardCsPin))
	{
#if defined(SD_CARD_SUPPORT)
		if (paramCount >= 1)
		{
			uint8_t csPin = static_cast<uint8_t>(atoi(params[0].value));
			result = _configController->setSdCardCsPin(csPin);

			if (result == ConfigResult::InvalidPin)
			{
				char dbg[40];
				snprintf(dbg, sizeof(dbg), "SD CS pin %u blocked: %s", csPin,
					reinterpret_cast<const char*>(PinGuard::reasonString(PinGuard::validate(csPin, PinUse::SpiCs))));
				sender->sendDebug(dbg, "C32");
			}
		}
		else
		{
			result = ConfigResult::InvalidParameter;
		}
#else
		sendAckErr(sender, command, F("SD card not supported"));
		return true;
#endif
	}
	else if (SystemFunctions::commandMatches(command, ConfigLightSensorThreshold))
	{
		if (paramCount == 1)
		{
			uint16_t threshold = static_cast<uint16_t>(atoi(params[0].value));
			result = _configController->setLightSensorThreshold(threshold);
		}
		else
		{
			result = ConfigResult::InvalidParameter;
		}
	}
#if defined(MQTT_SUPPORT)
	else if (command[0] == 'M' && strlen(command) >= 2)
	{
		// MQTT configuration commands (M0-M8)
		Config* config = _configController->getConfigPtr();

		if (config == nullptr)
		{
			result = ConfigResult::InvalidConfig;
		}
		else if (paramCount == 0)
		{
			// Query operation - similar to C16 WiFi State
			StringKeyValue param;

			if (SystemFunctions::commandMatches(command, MqttConfigEnable))
			{
				// M0 - MQTT Enabled
				strncpy(param.key, ValueParamName, sizeof(param.key));
				snprintf(param.value, sizeof(param.value), "%d", config->mqtt.enabled ? 1 : 0);
				sendAckOk(sender, command, &param);
				return true;
			}
			else if (SystemFunctions::commandMatches(command, MqttConfigBroker))
			{
				// M1 - MQTT Broker
				strncpy(param.key, ValueParamName, sizeof(param.key));
				strncpy(param.value, config->mqtt.broker, sizeof(param.value));
				sendAckOk(sender, command, &param);
				return true;
			}
			else if (SystemFunctions::commandMatches(command, MqttConfigPort))
			{
				// M2 - MQTT Port
				strncpy(param.key, ValueParamName, sizeof(param.key));
				snprintf(param.value, sizeof(param.value), "%u", config->mqtt.port);
				sendAckOk(sender, command, &param);
				return true;
			}
			else if (SystemFunctions::commandMatches(command, MqttConfigUsername))
			{
				// M3 - MQTT Username
				strncpy(param.key, ValueParamName, sizeof(param.key));
				strncpy(param.value, config->mqtt.username, sizeof(param.value));
				param.value[sizeof(param.value) - 1] = '\0';
				sendAckOk(sender, command, &param);
				return true;
			}
			else if (SystemFunctions::commandMatches(command, MqttConfigPassword))
			{
				// M4 - MQTT Password
				strncpy(param.key, ValueParamName, sizeof(param.key));
				strncpy(param.value, config->mqtt.password, sizeof(param.value));
				param.value[sizeof(param.value) - 1] = '\0';
				sendAckOk(sender, command, &param);
				return true;
			}
			else if (SystemFunctions::commandMatches(command, MqttConfigDeviceId))
			{
				// M5 - MQTT Device ID
				strncpy(param.key, ValueParamName, sizeof(param.key));
				strncpy(param.value, config->mqtt.deviceId, sizeof(param.value));
				sendAckOk(sender, command, &param);
				return true;
			}
			else if (SystemFunctions::commandMatches(command, MqttConfigHADiscovery))
			{
				// M6 - HA Discovery Enabled
				strncpy(param.key, ValueParamName, sizeof(param.key));
				snprintf(param.value, sizeof(param.value), "%d", config->mqtt.useHomeAssistantDiscovery ? 1 : 0);
				sendAckOk(sender, command, &param);
				return true;
			}
			else if (SystemFunctions::commandMatches(command, MqttConfigKeepAlive))
			{
				// M7 - Keep Alive Interval
				strncpy(param.key, ValueParamName, sizeof(param.key));
				snprintf(param.value, sizeof(param.value), "%u", config->mqtt.keepAliveInterval);
				sendAckOk(sender, command, &param);
				return true;
			}
			else if (SystemFunctions::commandMatches(command, MqttConfigState))
			{
				// M8 - MQTT Connection State
				strncpy(param.key, ValueParamName, sizeof(param.key));

				// Get actual connection state from MQTTController if available
				bool isConnected = false;
				if (_mqttController != nullptr)
				{
					isConnected = _mqttController->isConnected();
				}
				else
				{
					// Fallback to config enabled state if controller not available
					isConnected = config->mqtt.enabled;
				}

				snprintf(param.value, sizeof(param.value), "%d", isConnected ? 1 : 0);
				sendAckOk(sender, command, &param);
				return true;
			}
			else if (SystemFunctions::commandMatches(command, MqttConfigDiscoveryPrefix))
			{
				// M9 - Discovery Prefix
				strncpy(param.key, ValueParamName, sizeof(param.key));
				strncpy(param.value, config->mqtt.discoveryPrefix, sizeof(param.value));
				param.value[sizeof(param.value) - 1] = '\0';
				sendAckOk(sender, command, &param);
				return true;
			}
			else
			{
				result = ConfigResult::InvalidCommand;
			}
		}
		else
		{
			// Set operation - delegate to MQTTConfigCommandHandler
			if (_mqttConfigHandler != nullptr)
			{
				const char* paramStr = params[0].value;

				if (_mqttConfigHandler->processCommand(command, paramStr))
				{
					result = ConfigResult::Success;
				}
				else
				{
					result = ConfigResult::InvalidParameter;
				}
			}
			else
			{
				result = ConfigResult::InvalidCommand;
			}
		}
	}
#endif
	else
	{
		result = ConfigResult::InvalidCommand;
	}

	switch (result)
	{
	case ConfigResult::Success:
		break;
	case ConfigResult::InvalidRelay:
		sendAckErr(sender, command, F("Index out of range"), &params[0]);
		return true;
	case ConfigResult::TooLong:
		sendAckErr(sender, command, F("Name too long"), &params[0]);
		return true;
	case ConfigResult::MissingName:
		sendAckErr(sender, command, F("Missing name"), &params[0]);
		return true;
	case ConfigResult::InvalidConfig:
		sendAckErr(sender, command, F("Config not available"), &params[0]);
		return true;
	case ConfigResult::InvalidCommand:
		sendAckErr(sender, command, F("Invalid command"), &params[0]);
		return true;
	case ConfigResult::InvalidParameter:
		sendAckErr(sender, command, F("Invalid parameter"), &params[0]);
		return true;
	case ConfigResult::InvalidPin:
		sendAckErr(sender, command, F("Invalid pin"), &params[0]);
		return true;
	case ConfigResult::BluetoothInitFailed:
		sendAckErr(sender, command, F("Bluetooth init failed"), &params[0]);
		return true;
	case ConfigResult::WifiInitFailed:
		sendAckErr(sender, command, F("WiFi init failed"), &params[0]);
		return true;
	default:
		sendAckErr(sender, command, F("Unknown error"), &params[0]);
		return true;
	}

	sendAckOk(sender, command, &params[0]);

	return true;
}

#if defined(CARD_CONFIG_LOADER)
void ConfigCommandHandler::setSdCardConfigLoader(SdCardConfigLoader* sdCardConfigLoader)
{
	_sdCardConfigLoader = sdCardConfigLoader;
}
#endif

const char* const* ConfigCommandHandler::supportedCommands(size_t& count) const
{
	static const char* cmds[] = {
		ConfigSaveSettings, ConfigGetSettings, ConfigResetSettings,
		ConfigRename, ConfigMapHomeButton, ConfigXpdzTonePin,
	  ConfigSpiPins,
		ConfigBoatType, ConfigHw479RgbPins, ConfigSoundStartDelay,
		ConfigBluetoothEnable, ConfigWifiEnable, ConfigWifiMode, ConfigWifiSSID,
		ConfigWifiPassword, ConfigWifiPort, ConfigWifiState, ConfigWifiApIpAddress,
		ConfigRtcPins,
		ConfigAuthCommand,
#if defined(MQTT_SUPPORT)
		MqttConfigEnable, MqttConfigBroker, MqttConfigPort, MqttConfigUsername,
		MqttConfigPassword, MqttConfigDeviceId, MqttConfigHADiscovery, MqttConfigKeepAlive,
		MqttConfigState, MqttConfigDiscoveryPrefix,
#endif
		ConfigTimeZoneOffset, ConfigMmsi, ConfigCallSign, ConfigHomePort,
		ConfigLedColor, ConfigLedBrightness, ConfigLedAutoSwitch, ConfigLedEnable,
		ControlPanelTones,
		ConfigReloadFromSd, ConfigExportToSd, ConfigSdCardSpeed, ConfigSdCardCsPin,
		ConfigLightSensorThreshold
	};
	count = sizeof(cmds) / sizeof(cmds[0]);
	return cmds;
}
