SmartFuseBox/SmartFuseBox/PowerControlHub/ConfigController.h

/*
 * PowerControlHub
 * Copyright (C) 2025 Simon Carter (s1cart3r@gmail.com)
 *
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
 * You should have received a copy of the GNU General Public License
 * along with this program. If not, see <https://www.gnu.org/licenses/>.
 */
#pragma once

#include "Local.h"
#include "ConfigManager.h"
#include "SoundController.h"

// Forward declarations
class IBluetoothRadio;
class IWifiController;

enum class ConfigResult : uint8_t
{
	Success = 0,
	InvalidConfig = 1,
	Failed = 2,
	MissingName = 3,
	TooLong = 4,
	InvalidRelay = 5,
	InvalidCommand = 6,
	InvalidParameter = 7,
	BluetoothInitFailed = 8,
	WifiInitFailed = 9,
	InvalidPin = 10
};

class ConfigController
{
private:
	SoundController* _soundController;
	IBluetoothRadio* _bluetoothRadio;
	IWifiController* _wifiController;
	Config* _config;

	void updateSoundControllerConfig();
public:

	ConfigController(SoundController* soundController,
		IBluetoothRadio* bluetoothRadio,
		IWifiController* wifiController);

	Config* getConfigPtr();
	ConfigResult save();
	ConfigResult reset();
	ConfigResult rename(const char* name);
	ConfigResult mapHomeButton(const uint8_t homeButtonIndex, const uint8_t relayIndex);
	ConfigResult setLocationType(const uint8_t vesselType);
	ConfigResult setsoundDelayStart(const uint16_t delayMilliSeconds);
	ConfigResult setBluetoothEnabled(const bool enabled);
	ConfigResult setWifiEnabled(const bool enabled);
	ConfigResult setWifiAccessMode(const WifiMode accessMode);
	ConfigResult setWifiSsid(const char* ssid);
	ConfigResult setWifiPassword(const char* password);
	ConfigResult setWifiPort(const uint16_t port);
	ConfigResult setWifiIpAddress(const char* ipAddress);
	ConfigResult setTimezoneOffset(const int8_t offset);
	ConfigResult setMmsi(const char* mmsi);
	ConfigResult setCallSign(const char* callSign);
	ConfigResult setHomePort(const char* homePort);
	ConfigResult setLedColor(const uint8_t type, const uint8_t colorSet, const uint8_t r, const uint8_t g, const uint8_t b);
	ConfigResult setLedBrightness(const uint8_t type, const uint8_t brightness);
	ConfigResult setLedAutoSwitch(const bool enabled);
	ConfigResult setLedEnableStates(const bool gps, const bool warning, const bool system);
	ConfigResult setControlPanelTones(const uint8_t type, const uint8_t preset, const uint16_t toneHz, const uint16_t durationMs, const uint32_t repeatMs);
	ConfigResult setSdCardInitializeSpeed(const uint8_t speedMhz);
	ConfigResult setSdCardCsPin(const uint8_t csPin);
	ConfigResult setSpiPins(const uint8_t sckPin, const uint8_t mosiPin, const uint8_t misoPin);
	ConfigResult setLightSensorThreshold(const uint16_t threshold);
	ConfigResult setXpdzTonePin(const uint8_t pin);
	ConfigResult setHw479RgbPins(const uint8_t rPin, const uint8_t gPin, const uint8_t bPin);
	ConfigResult setRtcPins(const uint8_t dataPin, const uint8_t clockPin, const uint8_t resetPin);
	ConfigResult setNextionEnabled(const bool enabled);
	ConfigResult setNextionHardwareSerial(const bool isHardwareSerial);
	ConfigResult setNextionRxPin(const uint8_t rxPin);
	ConfigResult setNextionTxPin(const uint8_t txPin);
	ConfigResult setNextionBaudRate(const uint32_t baudRate);
	ConfigResult setNextionUartNum(const uint8_t uartNum);

	// Network authentication helpers
	ConfigResult generateAuthKeys();
	ConfigResult setAuthEnabled(const bool enabled);
	ConfigResult setAuthApiKey(const char* apiKey);
	ConfigResult setAuthHmacKey(const char* hmacKey);
};
