SmartFuseBox/SmartFuseBox/PowerControlHub/BoardConfig.h

/*
 * PowerControlHub
 * Copyright (C) 2025 Simon Carter (s1cart3r@gmail.com)
 *
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
 * You should have received a copy of the GNU General Public License
 * along with this program. If not, see <https://www.gnu.org/licenses/>.
 */
#pragma once

/*
 * BoardConfig.h - framework-owned board capability table (do not edit)
 *
 * This file is included by Local.h and reads the board selection and feature
 * opt-ins defined there to derive capability flags, EEPROM sizing, and
 * scheduler support. It also enforces invalid-combination guards.
 *
 * To add a new board: add an entry to the EEPROM table and the WIFI_SUPPORT
 * block below. Local.h does not need to change.
 */

// ─── Board Conflict Guards ────────────────────────────────────────────────────
#if defined(ARDUINO_UNO_R4)
  #if defined(ESP32) || defined(ARDUINO_R4_MINIMA)
    #error "Multiple board types defined. Activate exactly one in Local.h."
  #endif
#endif

#if defined(ESP32)
  #if defined(ARDUINO_UNO_R4) || defined(ARDUINO_R4_MINIMA)
    #error "Multiple board types defined. Activate exactly one in Local.h."
  #endif
#endif

#if defined(ARDUINO_R4_MINIMA)
  #if defined(ARDUINO_UNO_R4) || defined(ESP32)
    #error "Multiple board types defined. Activate exactly one in Local.h."
  #endif
#endif

#if !defined(ARDUINO_UNO_R4) && !defined(ESP32) && !defined(ARDUINO_R4_MINIMA)
  #error "No board type defined. Activate one in Local.h (e.g. ARDUINO_UNO_R4)."
#endif


// ─── EEPROM Capacity Table ────────────────────────────────────────────────────
// Add new board entries here. Local.h does not need to change.
#if defined(ARDUINO_UNO_R4) || defined(ARDUINO_R4_MINIMA)
  #define EEPROM_CAPACITY_BYTES 8192
#elif defined(ESP32)
  #define EEPROM_CAPACITY_BYTES 16384
#else
  #define EEPROM_CAPACITY_BYTES 1024
  #define MAXIMUM_EVENTS 6
#endif

#if !defined(MAXIMUM_EVENTS)
  #define MAXIMUM_EVENTS 20
#endif


 // ─── ADC Resolution Table ─────────────────────────────────────────────────────
 // ADC_RESOLUTION_BITS  – native bit depth used by analogRead() on this board.
 // ADC_FULL_SCALE       – exclusive upper bound (2^bits); use as the divisor in
 //                        voltage calculations.
 // CONFIGURE_ADC        – defined when analogReadResolution() must be called at
 //                        boot to match ADC_RESOLUTION_BITS (not available on AVR).
#if defined(ESP32)
    #define ADC_RESOLUTION_BITS 12
    #define ADC_FULL_SCALE 4096
    #define CONFIGURE_ADC
#elif defined(ARDUINO_UNO_R4) || defined(ARDUINO_R4_MINIMA)
    #define ADC_RESOLUTION_BITS 14
    #define ADC_FULL_SCALE 16384
    #define CONFIGURE_ADC
#else
    // AVR (Mega 2560 etc.) — fixed 10-bit, analogReadResolution() not available
    #define ADC_RESOLUTION_BITS 10
    #define ADC_FULL_SCALE 1024
#endif


// ─── Derived: WiFi Support ────────────────────────────────────────────────────
#if defined(ARDUINO_UNO_R4) || defined(ESP32)
  #define WIFI_SUPPORT
#endif


// ─── Feature Combination Guards ───────────────────────────────────────────────
#if defined(MQTT_SUPPORT) && !defined(WIFI_SUPPORT)
  #error "MQTT_SUPPORT requires WIFI_SUPPORT. Enable a WiFi-capable board in Local.h."
#endif

#if defined(ARDUINO_UNO_R4) && defined(WIFI_SUPPORT) && defined(BLUETOOTH_SUPPORT)
  #error "WIFI_SUPPORT and BLUETOOTH_SUPPORT cannot both be active on Arduino Uno R4. Disable one in Local.h."
#endif

// ─── OTA Auto-Update Guard ───────────────────────────────────────────────────
// OTA requires ESP32 (Update library) and an active WiFi client connection.
// Silently strip the define on unsupported boards instead of erroring, so that
// the same Local.h can be used across board types without manual edits.
#if defined(OTA_AUTO_UPDATE)
  #if !defined(ESP32) || !defined(WIFI_SUPPORT)
    #undef OTA_AUTO_UPDATE
  #endif
#endif

// ─── Pin Guard ───────────────────────────────────────────────────────────────
// PinGuard selects ESP32 pin validation tables using IDF target macros
// (for example CONFIG_IDF_TARGET_ESP32S3 / CONFIG_IDF_TARGET_ESP32).
// Non-ESP32 boards get a no-op implementation.
#include "PinGuard.h"
