SmartFuseBox/SmartFuseBox/BoatControlPanel/BoatControlPanelConstants.h

#pragma once

constexpr uint8_t PinRtcClock = 5;
constexpr uint8_t PinRtcData = 6;
constexpr uint8_t PinRtcReset = 7;

constexpr uint8_t PinRgbRed = 4;
constexpr uint8_t PinRgbGreen = 3;
constexpr uint8_t PinRgbBlue = 2;
