SmartFuseBox/SmartFuseBox/StaticElectrics/Dht11SensorHandler.h

#pragma once


#include <SensorManager.h>
#include <SerialCommandManager.h>
#include <dht11.h>
#include "StaticElectricConstants.h"

constexpr unsigned long TempHumidityCheckMs = 2500;



// Convert uint64_t to char array (buffer must be at least 21 chars)
inline void uint64ToCharArray(uint64_t value, char* buffer) {
	if (value == 0) {
		buffer[0] = '0';
		buffer[1] = '\0';
		return;
	}

	char temp[21];
	int pos = 0;

	// Extract digits in reverse order
	while (value > 0) {
		temp[pos++] = '0' + (value % 10);
		value /= 10;
	}

	// Reverse into output buffer
	for (int i = 0; i < pos; i++) {
		buffer[i] = temp[pos - 1 - i];
	}
	buffer[pos] = '\0';
}

// Convenience wrapper for WarningType
inline String warningTypeToString(WarningType type) {
	char buffer[21];
	uint64ToCharArray(static_cast<uint64_t>(type), buffer);
	return String(buffer);
}


/**
 * @brief Sensor handler for DHT11 monitoring.
 *
 * Reads temperature and humidity sensor values, 
 * and reports readings to both link and computer serial connections.
 */
class Dht11SensorHandler : public BaseSensorHandler
{
private:
	SerialCommandManager* _commandMgrLink;
	SerialCommandManager* _commandMgrComputer;
	dht11 _dht11Sensor;
	const uint8_t _sensorPin;

protected:
	void initialize() override
	{
		pinMode(_sensorPin, INPUT);
	};

	unsigned long update() override
	{
		int result = _dht11Sensor.read(_sensorPin);

		if (result != DHTLIB_OK)
		{
			if (_commandMgrComputer)
			{
				if (_commandMgrLink)
				{
					_commandMgrLink->sendCommand(WarningAdd, warningTypeToString(WarningType::TemperatureSensorFailure) + F("=1"), "");
				}

				_commandMgrComputer->sendDebug(String(result), F("DHT11 Error"));
			}

			return TempHumidityCheckMs;
		}

		if (_commandMgrComputer)
		{
			_commandMgrComputer->sendDebug(String(_dht11Sensor.humidity, 1), F("Humidity"));
			_commandMgrComputer->sendDebug(String(_dht11Sensor.temperature, 1), F("Temperature"));
		}

		if (_commandMgrLink)
		{
			_commandMgrLink->sendCommand(WarningAdd, warningTypeToString(WarningType::TemperatureSensorFailure) + F("=0"), "");
		}

		float humidity = _dht11Sensor.humidity;
		float tempCelsius = _dht11Sensor.temperature;

		if (_commandMgrLink)
		{
			StringKeyValue params[] = { { "v", String(tempCelsius, 1) } };
			_commandMgrLink->sendCommand(SensorTemperature, "", "", params, 1);
			params->value = String(humidity, 0);
			_commandMgrLink->sendCommand(SensorHumidity, "", "", params, 1);
		}

		return TempHumidityCheckMs;
	};
public:
	Dht11SensorHandler(SerialCommandManager* commandManagerLink, SerialCommandManager* commandManagerComputer,
		uint8_t sensorPin)
		: _commandMgrLink(commandManagerLink), _commandMgrComputer(commandManagerComputer), _dht11Sensor(), _sensorPin(sensorPin)
	{
	};
};
