SmartFuseBox/SmartFuseBox/BoatControlPanel/EnvironmentPage.cpp

/*
 * SmartFuseBox
 * Copyright (C) 2025 Simon Carter (s1cart3r@gmail.com)
 *
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
 * You should have received a copy of the GNU General Public License
 * along with this program. If not, see <https://www.gnu.org/licenses/>.
 */

#include "EnvironmentPage.h"
#include "Environment.h"
#include "DateTimeManager.h"
#include "SunCalculator.h"
#include "SystemFunctions.h"

const char TextLowRisk[] PROGMEM = "Low";
const char TextWatch[] PROGMEM = "Watch";
const char TextHighRisk[] PROGMEM = "High";
const char TextNA[] PROGMEM = "N/A";
const char TextColdDamp[] PROGMEM = "Cold & Damp";
const char TextCold[] PROGMEM = "Cold";
const char TextWarmSticky[] PROGMEM = "Warm & Sticky";
const char TextHumid[] PROGMEM = "Humid";
const char TextComfortable[] PROGMEM = "Comfortable";
const char TextFair[] PROGMEM = "Fair";

constexpr char ControlSunriseTime[] = "t2";
constexpr char ControlSunsetTime[] = "t4";
constexpr char ControlTemperature[] = "t8";
constexpr char ControlTemperatureIndicator[] = "p5";
constexpr char ControlComfort[] = "t9";
constexpr char ControlComfortIndicator[] = "p3";
constexpr char ControlHumidity[] = "t5";
constexpr char ControlHumidityIndicator[] = "p4";
constexpr char ControlDewPoint[] = "t10";
constexpr char ControlDewPointIndicator[] = "p1";
constexpr char ControlCondensation[] = "t14";
constexpr char ControlCondensationIndicator[] = "p0";

// Nextion Names/Ids on current Page
constexpr uint8_t ButtonPrevious = 2;


EnvironmentPage::EnvironmentPage(Stream* serialPort,
    WarningManager* warningMgr,
    SerialCommandManager* commandMgrLink,
    SerialCommandManager* commandMgrComputer)
    : BaseBoatPage(serialPort, warningMgr, commandMgrLink, commandMgrComputer)
{
}

void EnvironmentPage::onEnterPage()
{
	updateHumidity();
	updateTemperature();
	updateLatLon();
}

void EnvironmentPage::begin()
{
    // not used just now
}

void EnvironmentPage::refresh(unsigned long now)
{
    (void)now;

}

// Handle touch events for buttons
void EnvironmentPage::handleTouch(uint8_t compId, uint8_t eventType)
{
    (void)eventType;

    switch (compId)
    {
    case ButtonPrevious:
        setPage(PageHome);
        return;
    }
}

void EnvironmentPage::handleExternalUpdate(uint8_t updateType, const void* data)
{
    // Call base class first to handle heartbeat ACKs
    BaseBoatPage::handleExternalUpdate(updateType, data);

    if (updateType == static_cast<uint8_t>(PageUpdateType::Temperature) && data != nullptr)
    {
        const FloatStateUpdate* update = static_cast<const FloatStateUpdate*>(data);
		_previousTemp = _lastTemp;
        _lastTemp = update->value;
		updateTemperature();
    }
    else if (updateType == static_cast<uint8_t>(PageUpdateType::Humidity) && data != nullptr)
    {
        const UInt16Update* update = static_cast<const UInt16Update*>(data);
		_previousHumidity = _lastHumidity;
        _lastHumidity = static_cast<float>(update->value);
		updateHumidity();
    }
    else if (updateType == static_cast<uint8_t>(PageUpdateType::GpsLatitude) && data != nullptr)
    {
        // FloatStateUpdate is used for GPS lat/lon notifications
        const FloatStateUpdate* update = static_cast<const FloatStateUpdate*>(data);
        _lastLatitude = update->value;
        updateLatLon();
    }
    else if (updateType == static_cast<uint8_t>(PageUpdateType::GpsLongitude) && data != nullptr)
    {
        const FloatStateUpdate* update = static_cast<const FloatStateUpdate*>(data);
        _lastLongitude = update->value;
        updateLatLon();
    }
}

void EnvironmentPage::updateTemperature()
{
    if (isnan(_lastTemp))
    {
        sendText(ControlTemperature, NoValueText);
		setPicture(ControlTemperatureIndicator, ImageQuestionMark);
        return;
    }

    char cmd[14];
    dtostrf(_lastTemp, 4, 1, cmd);

    size_t len = strlen(cmd);

    // Append degree symbol (character 176) and "C"
    if (len + 2 < sizeof(cmd))
    {
        cmd[len] = (char)176;
        cmd[len + 1] = '\0';
        strcat(cmd, CelsiusSuffix);
    }

	// update direction indicator increasing/decreasing/same but only within 0.5 degree change
    if (_lastTemp > _previousTemp)
    {
        setPicture(ControlTemperatureIndicator, ImageUpArrow);
    }
    else if (_previousTemp > _lastTemp)
    {
        setPicture(ControlTemperatureIndicator, ImageDownArrow);
    }
    else
    {
        setPicture(ControlTemperatureIndicator, ImageInwardArrow);
    }

    sendText(ControlTemperature, cmd);
    updateCondensation();
    updateDewPoint();
}

void EnvironmentPage::updateHumidity()
{
    if (isnan(_lastHumidity))
    {
        sendText(ControlHumidity, NoValueText);
		setPicture(ControlHumidityIndicator, ImageQuestionMark);
        return;
    }

    char cmd[10];
    dtostrf(_lastHumidity, 4, 1, cmd);

    size_t len = strlen(cmd);

    if (len + strlen(PercentSuffix) < sizeof(cmd))
    {
        strcpy(cmd + len, PercentSuffix);
    }

    // update direction indicator increasing/decreasing/same
	if (_lastHumidity > _previousHumidity)
    {
        setPicture(ControlHumidityIndicator, ImageUpArrow);
    }
    else if (_previousHumidity > _lastHumidity)
    {
        setPicture(ControlHumidityIndicator, ImageDownArrow);
    }
    else
    {
        setPicture(ControlHumidityIndicator, ImageInwardArrow);
    }

    sendText(ControlHumidity, cmd);
    updateCondensation();
    updateDewPoint();
}

void EnvironmentPage::updateLatLon()
{
    if (isnan(_lastLatitude) || isnan(_lastLongitude))
    {
        return;
    }

    updateSunriseSunset();
}

void EnvironmentPage::updateSunriseSunset()
{
	Config* config = getConfig();

	if (config == nullptr)
    {
        return;
    }

    SunTimes suntimes = SunCalculator::calculateSunTimes(_lastLatitude, _lastLongitude,
        DateTimeManager::getYear(),
        DateTimeManager::getMonth(),
        DateTimeManager::getDay(),
		config->system.timezoneOffset);

    char cmd[14];

	if (!suntimes.isValid)
    {
		SystemFunctions::progmemToBuffer(TextNA, cmd, sizeof(cmd));
        sendText(ControlSunriseTime, cmd);
        sendText(ControlSunsetTime, cmd);
        return;
    }


    // Wrap hours to 0-23 range
    int sunriseHour = (int)suntimes.sunrise;
    if (sunriseHour < 0) sunriseHour += 24;
    if (sunriseHour >= 24) sunriseHour -= 24;

    int sunriseMin = (int)((suntimes.sunrise - (int)suntimes.sunrise) * 60);
    if (sunriseMin < 0) sunriseMin += 60;

    snprintf_P(cmd, sizeof(cmd), PSTR("%02d:%02d"), sunriseHour, sunriseMin);
    sendText(ControlSunriseTime, cmd);

    int sunsetHour = (int)suntimes.sunset;
    if (sunsetHour < 0) sunsetHour += 24;
    if (sunsetHour >= 24) sunsetHour -= 24;

    int sunsetMin = (int)((suntimes.sunset - (int)suntimes.sunset) * 60);
    if (sunsetMin < 0) sunsetMin += 60;

    snprintf_P(cmd, sizeof(cmd), PSTR("%02d:%02d"), sunsetHour, sunsetMin);
    sendText(ControlSunsetTime, cmd);
}

void EnvironmentPage::updateCondensation()
{
    double dewPt = Environment::dewPoint(_lastTemp, _lastHumidity);
    CondensationRisk risk = Environment::condensationRisk(_lastTemp, dewPt, false);
    char buffer[24];

    switch (risk)
    {
    case CondensationRisk::Low:
        setPicture(ControlCondensationIndicator, ImageGreenCircle);
		SystemFunctions::progmemToBuffer(TextLowRisk, buffer, sizeof(buffer));
        break;
    case CondensationRisk::Watch:
        setPicture(ControlCondensationIndicator, ImageOrangeCircle);
		SystemFunctions::progmemToBuffer(TextWatch, buffer, sizeof(buffer));
        break;
    case CondensationRisk::High:
        setPicture(ControlCondensationIndicator, ImageRedCircle);
        SystemFunctions::progmemToBuffer(TextHighRisk, buffer, sizeof(buffer));
        break;
	}

    sendText(ControlCondensation, buffer);
}

void EnvironmentPage::updateDewPoint()
{
    if (isnan(_lastTemp) || isnan(_lastHumidity))
    {
        sendText(ControlDewPoint, NoValueText);
        setPicture(ControlDewPointIndicator, ImageQuestionMark);
        return;
    }

    double dewPoint = Environment::dewPoint(_lastTemp, _lastHumidity);

    char cmd[10];
    dtostrf(dewPoint, 4, 1, cmd);

    size_t len = strlen(cmd);

    // Append degree symbol (character 176) and "C"
    if (len + 2 < sizeof(cmd))
    {
        cmd[len] = (char)176;
        cmd[len + 1] = '\0';
        strcat(cmd, CelsiusSuffix);
    }

	sendText(ControlDewPoint, cmd);

    updateComfortDescription(dewPoint);
}

void EnvironmentPage::updateComfortDescription(double dewPoint)
{
    char buffer[24];

    if (_lastTemp < 10 && _lastHumidity > 70)
    {
		SystemFunctions::progmemToBuffer(TextColdDamp, buffer, sizeof(buffer));
    }
    else if (_lastTemp < 12)
    {
		SystemFunctions::progmemToBuffer(TextCold, buffer, sizeof(buffer));
    }
    else if (_lastTemp > 26 && _lastHumidity > 65)
    {
		SystemFunctions::progmemToBuffer(TextWarmSticky, buffer, sizeof(buffer));
    }
    else if (dewPoint > 18)
    {
		SystemFunctions::progmemToBuffer(TextHumid, buffer, sizeof(buffer));
    }
    else if (_lastTemp >= 18 && _lastTemp <= 24 && _lastHumidity < 65)
    {
		SystemFunctions::progmemToBuffer(TextComfortable, buffer, sizeof(buffer));
    }
    else
    {
		SystemFunctions::progmemToBuffer(TextFair, buffer, sizeof(buffer));
    }

    sendText(ControlComfort, buffer);
}
